Prutsor/nlt-panel/firmware/include/constants.cpp

#include "constants.hpp"

const uint16_t STRIP_LEDS = 128;
const uint16_t STRIP_PIN = D6;
const uint16_t STRIP_TYPE = NEO_GRB + NEO_KHZ800;

const uint16_t NOISE_SCALE = 10000;
const uint16_t NOISE_SPEED = 10;

const uint32_t DIGIT_COLOR = Adafruit_NeoPixel::Color(255, 255, 255);

const uint32_t WHITE_COLOR = Adafruit_NeoPixel::Color(255, 255, 255);
const uint32_t BLACK_COLOR = Adafruit_NeoPixel::Color(0, 0, 0);
