Prutsor/nlt-panel/firmware/include/constants.hpp

#ifndef CONSTANTS_HPP
#define CONSTANTS_HPP

#include "Arduino.h"
#include <Adafruit_NeoPixel.h>

extern const uint16_t STRIP_LEDS;
extern const uint16_t STRIP_PIN;
extern const uint16_t STRIP_TYPE;

extern const uint16_t NOISE_SCALE;
extern const uint16_t NOISE_SPEED;

extern const uint32_t DIGIT_COLOR;

extern const uint32_t WHITE_COLOR;
extern const uint32_t BLACK_COLOR;

#endif  // CONSTANTS_HPP
